ethanjamesauto/drum-set/sim_frontend_protoboard_card/sim_frontend.asc

C1: cap; 0p
C2: cap; 68n
D1: diode; 1N4148
D2: diode; 1N4148
R1: res; 22K
R2: res; 100k
R3: res; 100k
V1: voltage; 3.3
V2: voltage; AC 1
Named nets: 0, Out, VCC
.ac dec 20 10 20k
