ethanjamesauto/drum-set/images/IMG_0992.jpg

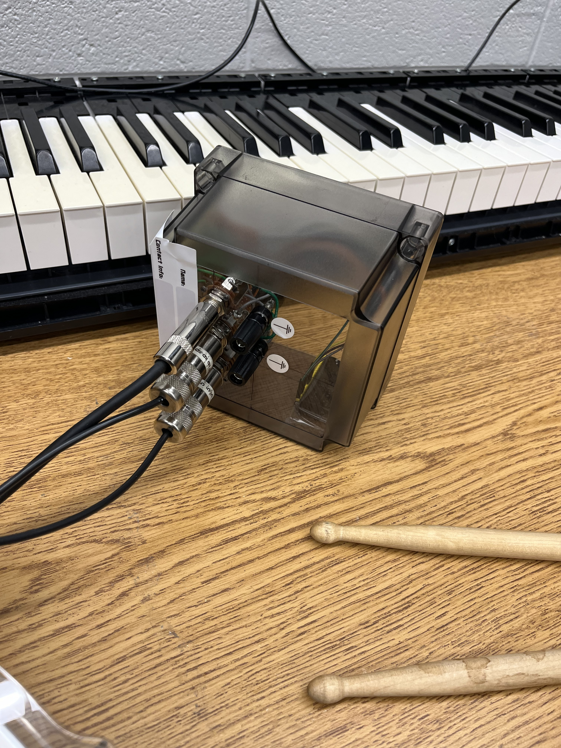
images/IMG_0992.jpg
