ethanjamesauto/drum-set/images/IMG_0993.jpg

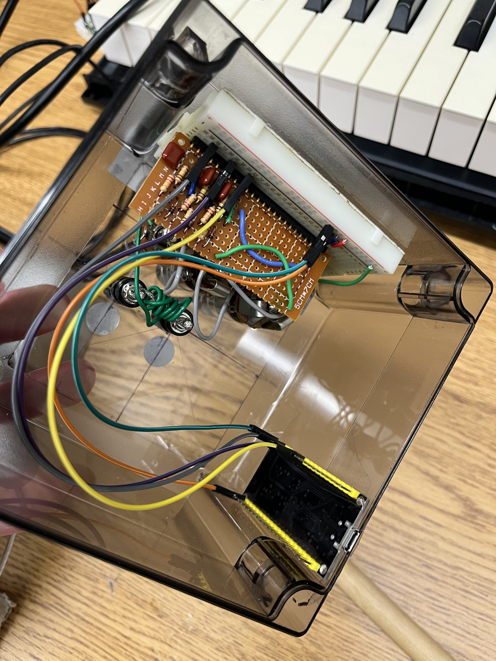
images/IMG_0993.jpg
